tynix5/no_fly_zone/firmware/no_fly_zone/Core/Src/app.c

#include "app.h"
#include "arm_math.h"
#include "main.h"
#include "stm32f446xx.h"
#include "stm32f4xx_hal.h"
#include "stm32f4xx_hal_gpio.h"
#include "stm32f4xx_hal_tim.h"
#include "usbd_cdc_if.h"
#include <stdio.h>
#include <stdbool.h>

#include "bldc.h"
#include "bms.h"
#include "dshot.h"
#include "lps25hb.h"
#include "lsm6ds3tr.h"
#include "madgwick.h"
#include "nrf24.h"
#include "quaternion.h"
#include "rf_structs.h"

#define BETA    0.2f
#define DELTA_T 1 / 1660.0 // replace with actual variable

#define RF_TX_ADDR 0xC2C2C2C2
#define RF_RX_ADDR 0xE7E7E7E7

#define RF_FAILSAFE_TIMEOUT_MS  100
#define IMU_FAILSAFE_TIMEOUT_MS 50
#define BAR_FAILSAFE_TIMEOUT_MS 1000

#define PKT_PER_ACK 10

#define ADC_RES_CNT 4096.0f

uint32_t micros_get_tick();
uint32_t millis_get_tick();
void delay_us(uint32_t delay);
void delay_ms(uint32_t delay);

nrf24_handle_t rx = {

    .ce_gpio = RF_CE_GPIO_Port,
    .ce_pin = RF_CE_Pin,
    .cs_gpio = RF_CS_GPIO_Port,
    .cs_pin = RF_CS_Pin,
    .delay_ms = delay_ms,
    .delay_us = delay_us,

    .power_level = NRF24_TX_PWR_0DBM,
    .data_rate = NRF24_DATARATE_2MBPS,
    .freq_ch = 110,           // 2400 MHz + 110 = 2.510 GHz

    .nrf24_irqs_t = {
        .rx_dr_en = true,
        .tx_ds_en = false,
        .max_rt_en = false,
    },
};

nrf24_pipe_t rx_pipe = {

    .address = RF_RX_ADDR,
    .ack = NRF24_AUTO_ACK_PAYLOAD,
    .payload_type = NRF24_PAYLOAD_DYNAMIC,
    .num = NRF24_PIPE0,
};

lps25_handle_t bar = {

    .cs_gpio = BAR_CS_GPIO_Port,
    .cs = BAR_CS_Pin,
    .delay_ms = delay_ms,

    .odr = BAR_ODR_7HZ,
    .it = BAR_INT_DRDY,

    .fifo_handle_t = {
        .mode = BAR_FIFO_BYPASS,
        .thresh = 31,
        .mov_smp = BAR_MOV_AVG_SMP_NONE,
    },
};

lsm6_handle_t imu = {

    .cs_gpio = IMU_CS_GPIO_Port,
    .cs = IMU_CS_Pin,
    .delay_ms = delay_ms,

    .gyro_handle_t = {
        .odr = IMU_ODR_G_1_66KHZ,
        .fs = IMU_FS_G_1000DPS,
        .filt = IMU_HPF_EN,
        .cutoff = IMU_HP_G_16MILHZ,
    },

    .accel_handle_t = {
        .odr = IMU_ODR_XL_1_66KHZ,
        .fs = IMU_FS_XL_8G,
        .filt = IMU_LPF_EN,
    },

    .fifo_handle_t = {
        .mode = IMU_FIFO_BYPASS,
        .odr = IMU_ODR_FIFO_DISABLE,
    },

    // accelerometer and gyroscope should trigger at about the same time (due to same ODR)
    .int_handle_t = {
        .int1 = IMU_INT1_DRDY_G,
        .int2 = IMU_INT2_NONE,
    }
};

bms_handle_t bms = {
    .type = BMS_LIPO_TYPE,
    .cell_cnt = 4,
    .div = 6,
    .v_ref = 3.3,
};

bldc_handle_t bldc;
madgwick_state_t state;

volatile bool rf_dr = false, imu_dr = false, bar_dr = false;
volatile uint32_t last_pkt_tick_ms, last_bar_tick_ms, last_imu_tick_us;
uint32_t this_imu_tick_us;

IWDG_HandleTypeDef * iwdg;
TIM_HandleTypeDef *tim_us_l, *tim_us_h;

// sense_adc[0]: VBAT_SENSE
// sense_adc[1]: CURR_SENSE
uint16_t sense_adc[2];

/***********************************************************************************************/
typedef enum : uint8_t
{
    FAILSAFE_TYPE_RF = 1,
    FAILSAFE_TYPE_IMU = 2,
    FAILSAFE_TYPE_BAR = 4,
    FAILSAFE_TYPE_REMOTE = 8
} failsafe_type_t;

failsafe_type_t failsafe_cause = 0;
/***********************************************************************************************/

arm_state_t arm_state_quad = ARM_STATE_DISARMED;

static void construct_ack(rf_ack_params_t * ack);
void bms_callback(bms_handle_t * bms, bms_event_t event);

void app_init(ADC_HandleTypeDef * hadc,
              SPI_HandleTypeDef * hspi_sensor,
              SPI_HandleTypeDef * hspi_rf,
              TIM_HandleTypeDef * htim2_motor,
              TIM_HandleTypeDef * htim_adc,
              TIM_HandleTypeDef * htim5_motor,
              TIM_HandleTypeDef * htim_us_l,
              TIM_HandleTypeDef * htim_us_h,
              IWDG_HandleTypeDef * hiwdg)
{
    // deselect all slaves at start
    HAL_GPIO_WritePin(IMU_CS_GPIO_Port, IMU_CS_Pin, GPIO_PIN_SET);
    HAL_GPIO_WritePin(BAR_CS_GPIO_Port, BAR_CS_Pin, GPIO_PIN_SET);

    // all motors no pwm
    HAL_GPIO_WritePin(GPIOA, GPIO_PIN_0, GPIO_PIN_RESET);
    HAL_GPIO_WritePin(GPIOA, GPIO_PIN_1, GPIO_PIN_RESET);
    HAL_GPIO_WritePin(GPIOA, GPIO_PIN_2, GPIO_PIN_RESET);
    HAL_GPIO_WritePin(GPIOA, GPIO_PIN_3, GPIO_PIN_RESET);

    tim_us_h = htim_us_h;
    tim_us_l = htim_us_l;
    rx.hspi = hspi_rf;
    bar.hspi = hspi_sensor;
    imu.hspi = hspi_sensor;
    iwdg = hiwdg;

    /********************************************* Configure nRF24l01 *****************************************/
    HAL_TIM_Base_Start(htim_us_l); // start microsecond timer for rf_init()
    HAL_TIM_Base_Start(htim_us_h); // start microsecond timer for rf_init()

    if (nrf24_init(&rx) == NRF24_OK)
        HAL_GPIO_WritePin(STAT1_GPIO_Port, STAT1_Pin, GPIO_PIN_SET);

    // move into same check as nrf24_init
    nrf24_open_rx_pipe(&rx, &rx_pipe);
    /**********************************************************************************************************/

    /******************************************** Configure barometer *****************************************/
    if (bar_init(&bar) == STATUS_OK)
        HAL_GPIO_WritePin(STAT2_GPIO_Port, STAT2_Pin, GPIO_PIN_SET);
    /**********************************************************************************************************/

    /*********************************************** Configure IMU ********************************************/
    if (imu_init(&imu) == STATUS_OK)
        HAL_GPIO_WritePin(STAT3_GPIO_Port, STAT3_Pin, GPIO_PIN_SET);
    /**********************************************************************************************************/

    delay_ms(1000);

    HAL_GPIO_WritePin(STAT1_GPIO_Port, STAT1_Pin, GPIO_PIN_RESET);
    HAL_GPIO_WritePin(STAT2_GPIO_Port, STAT2_Pin, GPIO_PIN_RESET);
    HAL_GPIO_WritePin(STAT3_GPIO_Port, STAT3_Pin, GPIO_PIN_RESET);

    /******************************************** Configure Watchdog ******************************************/
    hiwdg->Instance = IWDG;
    hiwdg->Init.Prescaler = IWDG_PRESCALER_4;
    hiwdg->Init.Reload = 3999;
    HAL_IWDG_Init(hiwdg); // T = 0.5s
    /**********************************************************************************************************/

    /***************************************** Configure DShot channels ***************************************/
    bldc_init(&bldc, htim2_motor, htim5_motor);
    bldc_enable(&bldc);
    /**********************************************************************************************************/

    /************************************** Configure battery management **************************************/
    // uncomment when battery is plugged in
    // bms_init(&bms, bms_callback);
    /**********************************************************************************************************/

    /**************************************** Initiate Madgwick Filter ****************************************/
    madgwick_init(&state);
    /**********************************************************************************************************/

    /************************************** Configure and Start ADC + DMA *************************************/
    // make sure this is working
    HAL_ADC_Start_DMA(hadc, (uint32_t *)sense_adc, 2); // enable ADC conversion for VBAT_SENSE and CURR_SENSE
    HAL_TIM_Base_Start(htim_adc);                      // start triggering ADC (T = 0.2s)
    /**********************************************************************************************************/

    nrf24_listen_it(&rx);

    last_pkt_tick_ms = last_bar_tick_ms = millis_get_tick();
    last_imu_tick_us = this_imu_tick_us = micros_get_tick();
}

void app(void)
{
    uint32_t pkt_cnt = 0;

    rf_packet_params_t pkt;
    rf_ack_params_t ack;

    const float k_att = 10.0;

    bool has_been_disarmed = 0;

    while (1)
    {
        HAL_IWDG_Refresh(iwdg);

        if (rf_dr)
        {
            rf_dr = false;

            construct_ack(&ack);

            rf_packet_params_t temp;
            uint8_t temp_size;

            nrf24_pipe_num_t pipe_num;

            // send acknowlegment every 10 packets
            if (pkt_cnt % PKT_PER_ACK == 0)
                nrf24_receive(&rx, (uint8_t *)&ack, sizeof(rf_ack_params_t), (uint8_t *)&temp, &temp_size, &pipe_num);
            else
                nrf24_receive(&rx, (uint8_t *)&ack, 0, (uint8_t *)&temp, &temp_size, &pipe_num);

            // discard packet if size doesnt match or keys dont match
            // copy to a valid packet if available
            if (temp_size == sizeof(rf_packet_params_t))
            {
                pkt_cnt++;

                /*
                char buff[50];
                uint32_t len = sprintf(buff, "Received pkt %d at t: %d\n", temp.throttle, last_pkt_tick_ms);
                CDC_Transmit_FS(buff, len);

                if (last_pid != temp.throttle - 1 && pkt_cnt != 1)
                {
                    len = sprintf(buff, "Missed pkt %d\n", temp.throttle - 1);
                    CDC_Transmit_FS(buff, len);
                }

                last_pid = temp.throttle;
                */

                switch (temp.key)
                {
                case DISARMED_KEY:
                    memcpy((uint8_t *)&pkt, (uint8_t *)&temp, sizeof(rf_packet_params_t));
                    has_been_disarmed = true;
                    // do not go into disarm mode if something has failed
                    if (arm_state_quad != ARM_STATE_FAILSAFE)
                        arm_state_quad = ARM_STATE_DISARMED;
                    break;
                case ARMED_KEY:
                    memcpy((uint8_t *)&pkt, (uint8_t *)&temp, sizeof(rf_packet_params_t));
                    // prevent quadcopter from arming if it has never seen a disarmed
                    // packet
                    if (has_been_disarmed && arm_state_quad != ARM_STATE_FAILSAFE)
                        arm_state_quad = ARM_STATE_ARMED;
                    break;
                case FAILSAFE_KEY:
                    memcpy((uint8_t *)&pkt, (uint8_t *)&temp, sizeof(rf_packet_params_t));
                    arm_state_quad = ARM_STATE_FAILSAFE;
                    // remote type doesn't really make sense, wouldn't receive anything
                    // from remote if it failed
                    failsafe_cause |= FAILSAFE_TYPE_REMOTE;
                    break;
                default:
                    // invalid packet, ignore
                }
            }
            nrf24_listen_it(&rx);
        }

        if (imu_dr)
        {
            imu_dr = false;

            float a_x, a_y, a_z, w_x, w_y, w_z;

            // update orientation estimation
            imu_read_gyro_radps(&imu, &w_x, &w_y, &w_z);
            imu_read_accel_mps2(&imu, &a_x, &a_y, &a_z);

            float dt = (float)(this_imu_tick_us - last_imu_tick_us) / 1000000.0f; // convert sample delay from us to s
            madgwick_update(a_x, a_y, a_z, w_x, w_y, w_z, BETA, dt, &state);

            // char data[50];
            // uint32_t len = sprintf(data, "%d, Diff = %d, Time(ms): %d\n", this_imu_tick_us, this_imu_tick_us - last_imu_tick_us, millis_get_tick());
            // CDC_Transmit_FS((uint8_t *)data, len);

            // stream orientation over USB (for debugging)
            // float data[] = { state._q_state.q1, state._q_state.q2, state._q_state.q3, state._q_state.q4 };
            // CDC_Transmit_FS((uint8_t *)data, sizeof(data));

            last_imu_tick_us = this_imu_tick_us;
        }

        if (bar_dr)
        {
            bar_dr = false;

            float hpa;
            bar_read_press_hpa(&bar, &hpa);
        }

        // if quadcopter sensors or RF communication is disrupted, go into failsafe
        // mode RF can only go into failsafe if previous communication has been
        // established
        uint32_t tick_ms = millis_get_tick();
        uint32_t tick_us = micros_get_tick();

        // save atomic copies before doing timeout checks
        // since it is possible for last_*_tick to change between >= check and *_FAILSAFE_TIMEOUT_MS check
        uint32_t last_pkt_tick_ms_local = last_pkt_tick_ms;
        uint32_t last_imu_tick_us_local = last_imu_tick_us;
        uint32_t last_bar_tick_ms_local = last_bar_tick_ms;

        // make sure tick_ms is > than last_tick_ms in case interrupt occurs between read and check
        // may not need the tick > last check
        if (tick_ms >= last_pkt_tick_ms_local && tick_ms - last_pkt_tick_ms_local > RF_FAILSAFE_TIMEOUT_MS && pkt_cnt != 0)
        {
            arm_state_quad = ARM_STATE_FAILSAFE;
            failsafe_cause |= FAILSAFE_TYPE_RF;

            /*
            char buff[100];
            uint32_t len;
            len = sprintf(buff, "Timeout at t: %d, dt: %d, Waiting for %d\n", tick_ms, tick_ms - last_pkt_tick_ms_local, last_pid + 1);
            CDC_Transmit_FS(buff, len);
            */
        }
        if (tick_us >= last_imu_tick_us_local && ((tick_us - last_imu_tick_us_local) / 1000) > IMU_FAILSAFE_TIMEOUT_MS)
        {
            arm_state_quad = ARM_STATE_FAILSAFE;
            failsafe_cause |= FAILSAFE_TYPE_IMU;
        }
        if (tick_ms >= last_bar_tick_ms_local && tick_ms - last_bar_tick_ms_local > BAR_FAILSAFE_TIMEOUT_MS)
        {
            arm_state_quad = ARM_STATE_FAILSAFE;
            failsafe_cause |= FAILSAFE_TYPE_BAR;
        }

        switch (arm_state_quad)
        {
        case ARM_STATE_DISARMED:
            // stop motors
            bldc_stop(&bldc);

            // uint16_t data[] = { 0, 0, 0, 0 };
            // CDC_Transmit_FS((uint8_t *)data, sizeof(data));

            HAL_GPIO_WritePin(STAT1_GPIO_Port, STAT1_Pin, GPIO_PIN_SET);
            HAL_GPIO_WritePin(STAT2_GPIO_Port, STAT2_Pin, GPIO_PIN_RESET);
            HAL_GPIO_WritePin(STAT3_GPIO_Port, STAT3_Pin, GPIO_PIN_RESET);
            break;

        case ARM_STATE_ARMED:

            // calculate quaternion error and convert to a rate error
            float w_x_err, w_y_err, w_z_err;
            quaternion_t q_des_sample = { .q1 = 1, .q2 = 0, .q3 = 0, .q4 = 0 };
            madgwick_curr_to_des(&state, q_des_sample, k_att, &w_x_err, &w_y_err, &w_z_err);
            // madgwick_curr_to_des(&state, pkt.q_des, k_att, &w_x_err, &w_y_err, &w_z_err);

            // run PID on ew --> place these into a matrix for cleaner math?
            // convert rate error to torque/speed commands
            float test_kp = 50.0;
            float tau_x = test_kp * w_x_err;
            float tau_y = test_kp * w_y_err;
            float tau_z = test_kp * w_z_err;

            // mix torque/speed commands
            float throttle_test = 1000;
            bldc_mix(&bldc, throttle_test, tau_x, tau_y, tau_z);
            // bldc_mix(&bldc, pkt.throttle, tau_x, tau_y, tau_z);

            bldc_send(&bldc);

            // uint16_t data[] = { bldc.throttles.speed_fl, bldc.throttles.speed_fr, bldc.throttles.speed_bl, bldc.throttles.speed_br };
            // CDC_Transmit_FS((uint8_t *)data, sizeof(data));

            HAL_GPIO_WritePin(STAT1_GPIO_Port, STAT1_Pin, GPIO_PIN_RESET);
            HAL_GPIO_WritePin(STAT2_GPIO_Port, STAT2_Pin, GPIO_PIN_SET);
            HAL_GPIO_WritePin(STAT3_GPIO_Port, STAT3_Pin, GPIO_PIN_RESET);

            break;

        case ARM_STATE_FAILSAFE:

            // immediately stop and disable motors
            bldc_stop(&bldc);
            bldc_disable(&bldc);

            HAL_GPIO_WritePin(STAT1_GPIO_Port, STAT1_Pin, GPIO_PIN_RESET);
            HAL_GPIO_WritePin(STAT2_GPIO_Port, STAT2_Pin, GPIO_PIN_RESET);
            HAL_GPIO_WritePin(STAT3_GPIO_Port, STAT3_Pin, GPIO_PIN_RESET);

            while (1)
            {
                // disable IMU, barometer, RF?
                // for initial versions, do not even attempt to recover from failure
                // must reset watchdog though

                if (failsafe_cause & FAILSAFE_TYPE_IMU)
                    HAL_GPIO_TogglePin(STAT1_GPIO_Port, STAT1_Pin);

                if (failsafe_cause & FAILSAFE_TYPE_BAR)
                    HAL_GPIO_TogglePin(STAT2_GPIO_Port, STAT2_Pin);

                if (failsafe_cause & FAILSAFE_TYPE_RF)
                    HAL_GPIO_TogglePin(STAT3_GPIO_Port, STAT3_Pin);

                HAL_IWDG_Refresh(iwdg);

                delay_ms(100);
            }

            break;

        default:
        }
    }
}

/************************************************* Interrupt Callbacks *****************************************************/
void HAL_GPIO_EXTI_Callback(uint16_t GPIO_Pin)
{
    // RF IRQ on falling edge
    if (GPIO_Pin == RF_IRQ_Pin)
    {
        rf_dr = true;
        last_pkt_tick_ms = millis_get_tick();
    }
    // IMU IRQ on rising edge
    if (GPIO_Pin == IMU_IRQ1_Pin)
    {
        imu_dr = true;
        this_imu_tick_us = micros_get_tick();
    }
    // BAR IRQ on rising edge
    if (GPIO_Pin == BAR_IRQ_Pin)
    {
        bar_dr = true;
        last_bar_tick_ms = millis_get_tick();
    }
}

void HAL_TIM_PWM_PulseFinishedCallback(TIM_HandleTypeDef * htim)
{
    // found in dshot.h
    dshot_complete_callback(&bldc.motor_fl, htim);
    dshot_complete_callback(&bldc.motor_fr, htim);
    dshot_complete_callback(&bldc.motor_bl, htim);
    dshot_complete_callback(&bldc.motor_br, htim);
}

void HAL_TIM_PWM_PulseFinishedHalfCpltCallback(TIM_HandleTypeDef * htim)
{
    // found in dshot.h
    dshot_half_complete_callback(&bldc.motor_fl, htim);
    dshot_half_complete_callback(&bldc.motor_fr, htim);
    dshot_half_complete_callback(&bldc.motor_bl, htim);
    dshot_half_complete_callback(&bldc.motor_br, htim);
}
/***************************************************************************************************************************/

static void construct_ack(rf_ack_params_t * ack)
{
    // float percent;
    // if (bms_update(&bms, (float)sense_adc[0] / ADC_RES_CNT, &percent) != STATUS_OK)
    //     return;

    float percent = 39.4;

    ack->quad_batt_lvl = (uint8_t)percent;

    switch (arm_state_quad)
    {
    case ARM_STATE_DISARMED:
        ack->key = DISARMED_KEY;
        break;
    case ARM_STATE_ARMED:
        ack->key = ARMED_KEY;
        break;
    case ARM_STATE_FAILSAFE:
    default:
        ack->key = FAILSAFE_KEY;
    }
}

void bms_callback(bms_handle_t * bms, bms_event_t event)
{
    // if battery dies, immediately go into failsafe mode to prevent full
    // discharge
    if (event == BMS_EVENT_CHARGE_EMPTY)
    {
        arm_state_quad = ARM_STATE_FAILSAFE;
    }
}

// chain 2 16-bit counters for a 32-bit counter
uint32_t micros_get_tick()
{
    uint16_t tim_low, tim_high;

    // check race conditions when doing non-atomic read over 2 registers
    do
    {
        tim_high = __HAL_TIM_GET_COUNTER(tim_us_h);
        tim_low = __HAL_TIM_GET_COUNTER(tim_us_l);

    } while (__HAL_TIM_GET_COUNTER(tim_us_h) != tim_high);

    return ((uint32_t)tim_high << 16) | (uint32_t)tim_low;
}

uint32_t millis_get_tick()
{
    return micros_get_tick() / 1000;
}

void delay_us(uint32_t delay)
{
    uint32_t start_us = micros_get_tick();
    while (micros_get_tick() - start_us < delay)
        ;
}

void delay_ms(uint32_t delay)
{
    delay_us(delay * 1000);
}
