tynix5/no_fly_zone/firmware/no_fly_zone_remote/Core/Inc/app.h

#ifndef APP_H_
#define APP_H_

#include <stdint.h>
#include "stm32l4xx_hal.h"
#include "stm32l4xx_hal_tim.h"

typedef struct
{
    uint16_t throttle;
    uint16_t yaw;
    uint16_t pitch;
    uint16_t roll;

} joystick_t;

void app_init(ADC_HandleTypeDef * hadc,
              DMA_HandleTypeDef * hdma,
              I2C_HandleTypeDef * hi2c,
              SPI_HandleTypeDef * hspi,
              TIM_HandleTypeDef * htim_adc,
              TIM_HandleTypeDef * henc,
              TIM_HandleTypeDef * htim_us_l);
void app(void);

#endif
